rileytuttle/order66keyboard/order66/order66.kicad_sch

## KiCad design order66/order66.kicad_sch (2025-06-20)

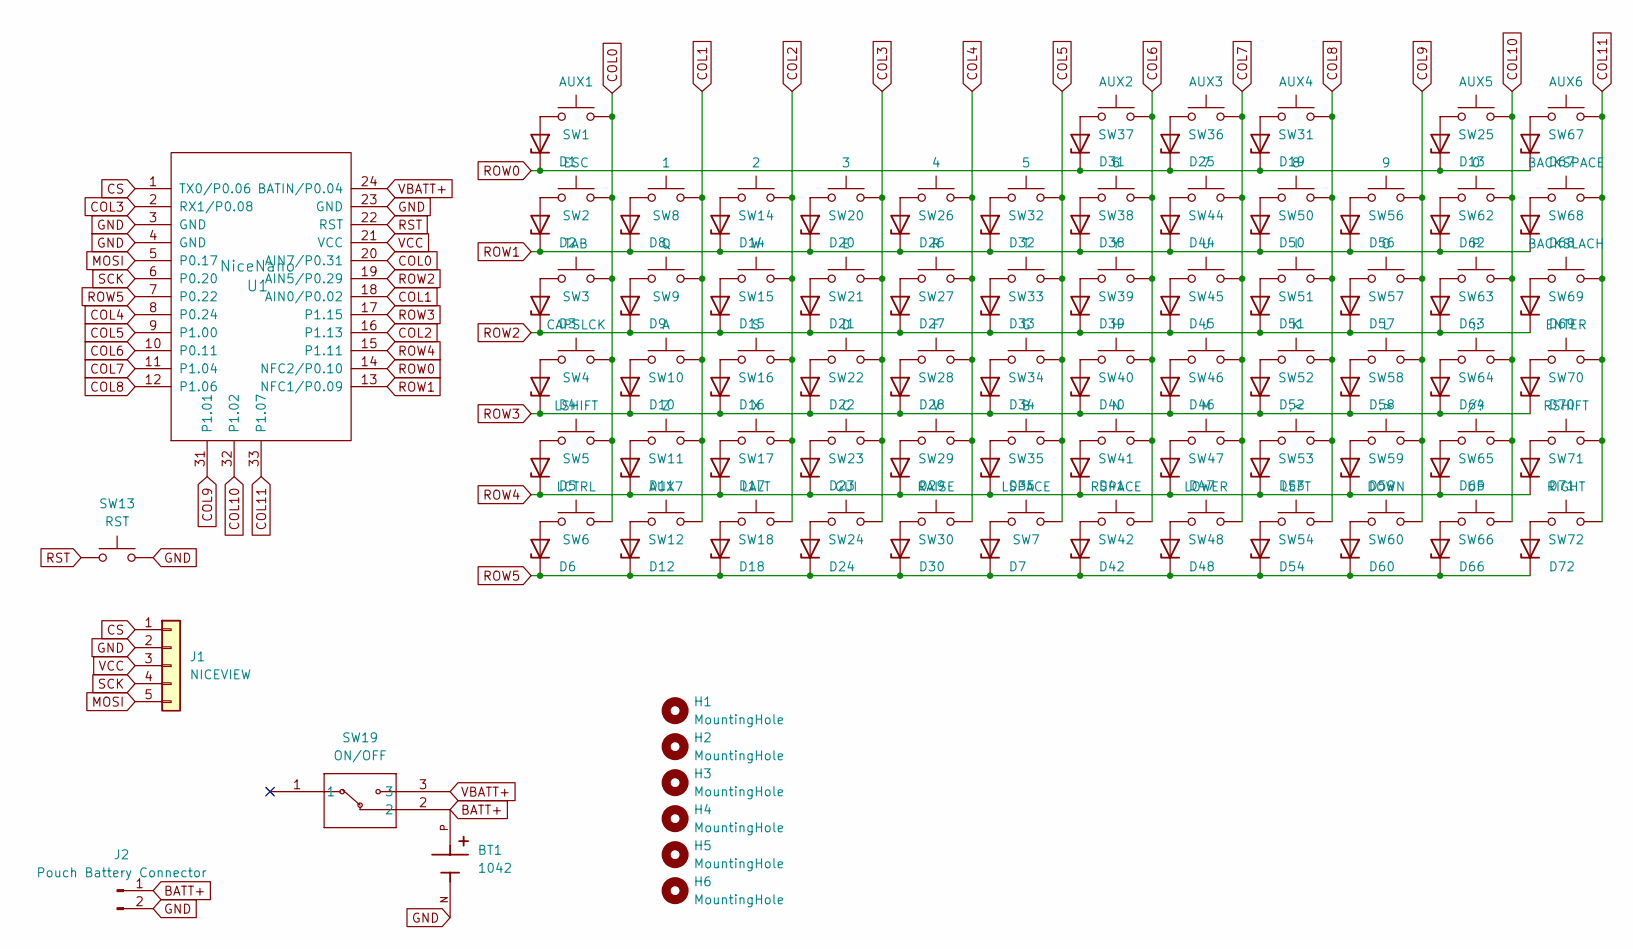
[picture p2: schematic order66.kicad_sch]

Parts:
BT1: 1042; BAT_1042; PARTREV E
D1, D2, D3, D4, D5, D6, D7, D8, D9, D10, D11, D12, D13, D14, D15, D16, D17, D18, D19, D20, D21, D22, D23, D24, D25, D26, D27, D28, D29, D30, D31, D32, D33, D34, D35, D38, D39, D40, D41, D42, D44, D45, D46, D47, D48, D50, D51, D52, D53, D54, D56, D57, D58, D59, D60, D62, D63, D64, D65, D66, D67, D68, D69, D70, D71, D72: 1N47xxA; D_SOD-123
H1, H2, H3, H4, H5, H6: MountingHole; MountingHole_2.7mm_M2.5
J1: NICEVIEW; PinHeader_1x05_P2.54mm_Vertical
J2: Pouch Battery Connector; JST_EH_S2B-EH_1x02_P2.50mm_Horizontal
SW1: AUX1; MX-Hotswap-1U
SW2: ESC; MX-Hotswap-1U
SW3: TAB; MX-Hotswap-1U
SW4: CAPSLCK; MX-Hotswap-1U
SW5: LSHIFT; MX-Hotswap-1U
SW6: LCTRL; MX-Hotswap-1U
SW7: LSPACE; MX-Hotswap-1U
SW8: 1; MX-Hotswap-1U
SW9: Q; MX-Hotswap-1U
SW10: A; MX-Hotswap-1U
SW11: Z; MX-Hotswap-1U
SW12: AUX7; MX-Hotswap-1U
SW13: RST; SW_SPST_TL3342
SW14: 2; MX-Hotswap-1U
SW15: W; MX-Hotswap-1U
SW16: S; MX-Hotswap-1U
SW17: X; MX-Hotswap-1U
SW18: LALT; MX-Hotswap-1U
SW19: ON/OFF; EG1206A_EWI
SW20: 3; MX-Hotswap-1U
SW21: E; MX-Hotswap-1U
SW22: D; MX-Hotswap-1U
SW23: C; MX-Hotswap-1U
SW24: GUI; MX-Hotswap-1U
SW25: AUX5; MX-Hotswap-1U
SW26: 4; MX-Hotswap-1U
SW27: R; MX-Hotswap-1U
SW28: F; MX-Hotswap-1U
SW29: V; MX-Hotswap-1U
SW30: RAISE; MX-Hotswap-1U
SW31: AUX4; MX-Hotswap-1U
SW32: 5; MX-Hotswap-1U
SW33: T; MX-Hotswap-1U
SW34: G; MX-Hotswap-1U
SW35: B; MX-Hotswap-1U
SW36: AUX3; MX-Hotswap-1U
SW37: AUX2; MX-Hotswap-1U
SW38: 6; MX-Hotswap-1U
SW39: Y; MX-Hotswap-1U
SW40: H; MX-Hotswap-1U
SW41: N; MX-Hotswap-1U
SW42: RSPACE; MX-Hotswap-1U
SW44: 7; MX-Hotswap-1U
SW45: U; MX-Hotswap-1U
SW46: J; MX-Hotswap-1U
SW47: M; MX-Hotswap-1U
SW48: LOWER; MX-Hotswap-1U
SW50: 8; MX-Hotswap-1U
SW51: I; MX-Hotswap-1U
SW52: K; MX-Hotswap-1U
SW53: ,<; MX-Hotswap-1U
SW54: LEFT; MX-Hotswap-1U
SW56: 9; MX-Hotswap-1U
SW57: O; MX-Hotswap-1U
SW58: L; MX-Hotswap-1U
SW59: .>; MX-Hotswap-1U
SW60: DOWN; MX-Hotswap-1U
SW62: 0; MX-Hotswap-1U
SW63: P; MX-Hotswap-1U
SW64: ;:; MX-Hotswap-1U
SW65: /?; MX-Hotswap-1U
SW66: UP; MX-Hotswap-1U
SW67: AUX6; MX-Hotswap-1U
SW68: BACKSPACE; MX-Hotswap-1U
SW69: BACKSLACH; MX-Hotswap-1U
SW70: ENTER; MX-Hotswap-1U
SW71: RSHIFT; MX-Hotswap-1U
SW72: RIGHT; MX-Hotswap-1U
U1: NiceNano; nice_nano

Connections:
BATT+: BT1.P, J2.1, SW19.2
COL0: SW1.2, SW2.2, SW3.2, SW4.2, SW5.2, SW6.2, U1.20 (AIN7/P0.31)
COL1: SW8.2, SW9.2, SW10.2, SW11.2, SW12.2, U1.18 (AIN0/P0.02)
COL2: SW14.2, SW15.2, SW16.2, SW17.2, SW18.2, U1.16 (P1.13)
COL3: SW20.2, SW21.2, SW22.2, SW23.2, SW24.2, U1.2 (RX1/P0.08)
COL4: SW26.2, SW27.2, SW28.2, SW29.2, SW30.2, U1.8 (P0.24)
COL5: SW7.2, SW32.2, SW33.2, SW34.2, SW35.2, U1.9 (P1.00)
COL6: SW37.2, SW38.2, SW39.2, SW40.2, SW41.2, SW42.2, U1.10 (P0.11)
COL7: SW36.2, SW44.2, SW45.2, SW46.2, SW47.2, SW48.2, U1.11 (P1.04)
COL8: SW31.2, SW50.2, SW51.2, SW52.2, SW53.2, SW54.2, U1.12 (P1.06)
COL9: SW56.2, SW57.2, SW58.2, SW59.2, SW60.2, U1.31 (P1.01)
COL10: SW25.2, SW62.2, SW63.2, SW64.2, SW65.2, SW66.2, U1.32 (P1.02)
COL11: SW67.2, SW68.2, SW69.2, SW70.2, SW71.2, SW72.2, U1.33 (P1.07)
CS: J1.1, U1.1 (TX0/P0.06)
GND: BT1.N, J1.2, J2.2, SW13.2, U1.3 (GND), U1.4 (GND), U1.23 (GND)
MOSI: J1.5, U1.5 (P0.17)
unnamed: D1.2 (A), SW1.1
unnamed: D2.2 (A), SW2.1
unnamed: D3.2 (A), SW3.1
unnamed: D4.2 (A), SW4.1
unnamed: D5.2 (A), SW5.1
unnamed: D6.2 (A), SW6.1
unnamed: D7.2 (A), SW7.1
unnamed: D8.2 (A), SW8.1
unnamed: D9.2 (A), SW9.1
unnamed: D10.2 (A), SW10.1
unnamed: D11.2 (A), SW11.1
unnamed: D12.2 (A), SW12.1
unnamed: D13.2 (A), SW25.1
unnamed: D14.2 (A), SW14.1
unnamed: D15.2 (A), SW15.1
unnamed: D16.2 (A), SW16.1
unnamed: D17.2 (A), SW17.1
unnamed: D18.2 (A), SW18.1
unnamed: D19.2 (A), SW31.1
unnamed: D20.2 (A), SW20.1
unnamed: D21.2 (A), SW21.1
unnamed: D22.2 (A), SW22.1
unnamed: D23.2 (A), SW23.1
unnamed: D24.2 (A), SW24.1
unnamed: D25.2 (A), SW36.1
unnamed: D26.2 (A), SW26.1
unnamed: D27.2 (A), SW27.1
unnamed: D28.2 (A), SW28.1
unnamed: D29.2 (A), SW29.1
unnamed: D30.2 (A), SW30.1
unnamed: D31.2 (A), SW37.1
unnamed: D32.2 (A), SW32.1
unnamed: D33.2 (A), SW33.1
unnamed: D34.2 (A), SW34.1
unnamed: D35.2 (A), SW35.1
unnamed: D38.2 (A), SW38.1
unnamed: D39.2 (A), SW39.1
unnamed: D40.2 (A), SW40.1
unnamed: D41.2 (A), SW41.1
unnamed: D42.2 (A), SW42.1
unnamed: D44.2 (A), SW44.1
unnamed: D45.2 (A), SW45.1
unnamed: D46.2 (A), SW46.1
unnamed: D47.2 (A), SW47.1
unnamed: D48.2 (A), SW48.1
unnamed: D50.2 (A), SW50.1
unnamed: D51.2 (A), SW51.1
unnamed: D52.2 (A), SW52.1
unnamed: D53.2 (A), SW53.1
unnamed: D54.2 (A), SW54.1
unnamed: D56.2 (A), SW56.1
unnamed: D57.2 (A), SW57.1
unnamed: D58.2 (A), SW58.1
unnamed: D59.2 (A), SW59.1
unnamed: D60.2 (A), SW60.1
unnamed: D62.2 (A), SW62.1
unnamed: D63.2 (A), SW63.1
unnamed: D64.2 (A), SW64.1
unnamed: D65.2 (A), SW65.1
unnamed: D66.2 (A), SW66.1
unnamed: D67.2 (A), SW67.1
unnamed: D68.2 (A), SW68.1
unnamed: D69.2 (A), SW69.1
unnamed: D70.2 (A), SW70.1
unnamed: D71.2 (A), SW71.1
unnamed: D72.2 (A), SW72.1
ROW0: D1.1 (K), D13.1 (K), D19.1 (K), D25.1 (K), D31.1 (K), D67.1 (K), U1.14 (NFC2/P0.10)
ROW1: D2.1 (K), D8.1 (K), D14.1 (K), D20.1 (K), D26.1 (K), D32.1 (K), D38.1 (K), D44.1 (K), D50.1 (K), D56.1 (K), D62.1 (K), D68.1 (K), U1.13 (NFC1/P0.09)
ROW2: D3.1 (K), D9.1 (K), D15.1 (K), D21.1 (K), D27.1 (K), D33.1 (K), D39.1 (K), D45.1 (K), D51.1 (K), D57.1 (K), D63.1 (K), D69.1 (K), U1.19 (AIN5/P0.29)
ROW3: D4.1 (K), D10.1 (K), D16.1 (K), D22.1 (K), D28.1 (K), D34.1 (K), D40.1 (K), D46.1 (K), D52.1 (K), D58.1 (K), D64.1 (K), D70.1 (K), U1.17 (P1.15)
ROW4: D5.1 (K), D11.1 (K), D17.1 (K), D23.1 (K), D29.1 (K), D35.1 (K), D41.1 (K), D47.1 (K), D53.1 (K), D59.1 (K), D65.1 (K), D71.1 (K), U1.15 (P1.11)
ROW5: D6.1 (K), D7.1 (K), D12.1 (K), D18.1 (K), D24.1 (K), D30.1 (K), D42.1 (K), D48.1 (K), D54.1 (K), D60.1 (K), D66.1 (K), D72.1 (K), U1.7 (P0.22)
RST: SW13.1, U1.22 (RST)
SCK: J1.4, U1.6 (P0.20)
VBATT+: SW19.3, U1.24 (BATIN/P0.04)
VCC: J1.3, U1.21 (VCC)
