rileytuttle/order66keyboard/build-photos/IMG_3756.jpg

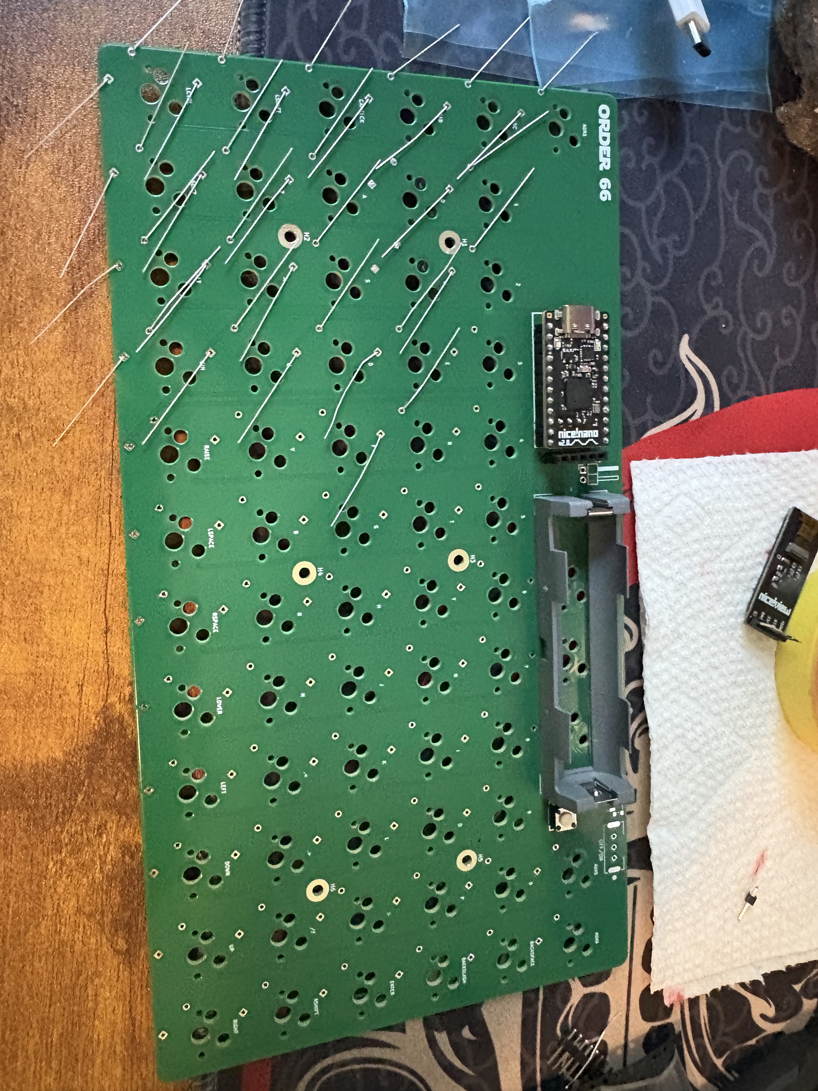
build-photos/IMG_3756.jpg
