rileytuttle/order66keyboard/build-photos/IMG_3759.jpg

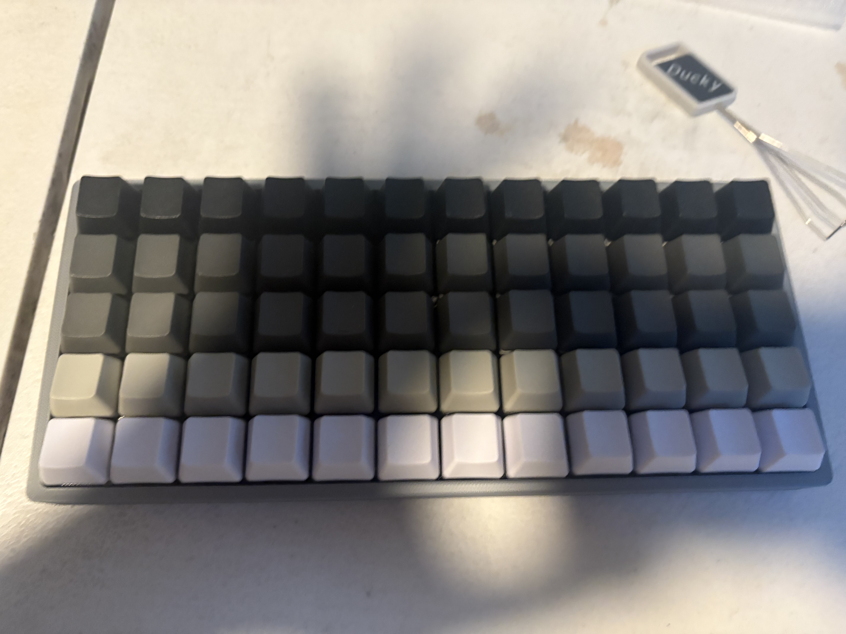
build-photos/IMG_3759.jpg
