rileytuttle/order66keyboard/build-photos/IMG_3760.jpg

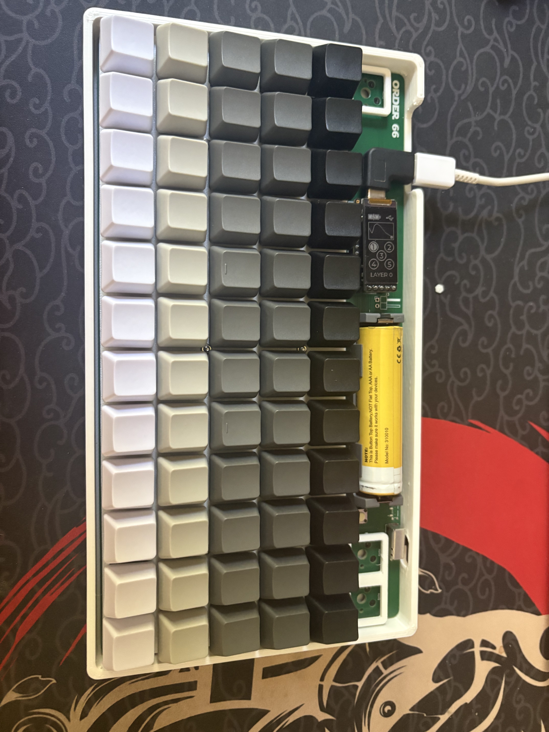
build-photos/IMG_3760.jpg
